fholgado/simhub-lumirank-display/nextion/BlueFlag.png

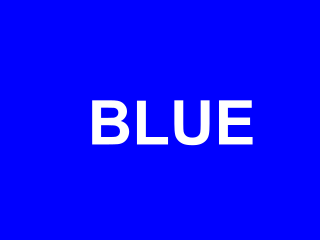
nextion/BlueFlag.png
