fholgado/simhub-lumirank-display/nextion/DoubleYellow.png

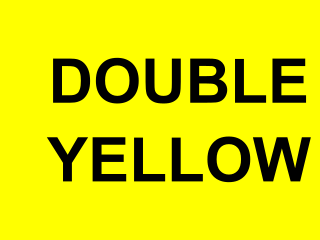
nextion/DoubleYellow.png
