fholgado/simhub-lumirank-display/nextion/Greenflag.png

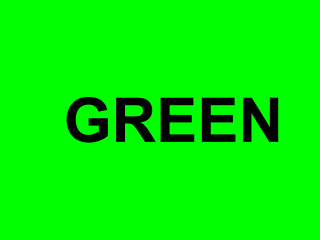
nextion/Greenflag.png
