fholgado/simhub-lumirank-display/nextion/ReadyScreen.png

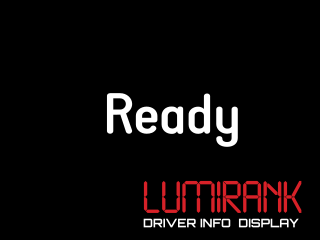
nextion/ReadyScreen.png
